tkmt25/chordimouse/circuit/chordimouse.kicad_sch

## KiCad design circuit/chordimouse.kicad_sch (2025-05-18)

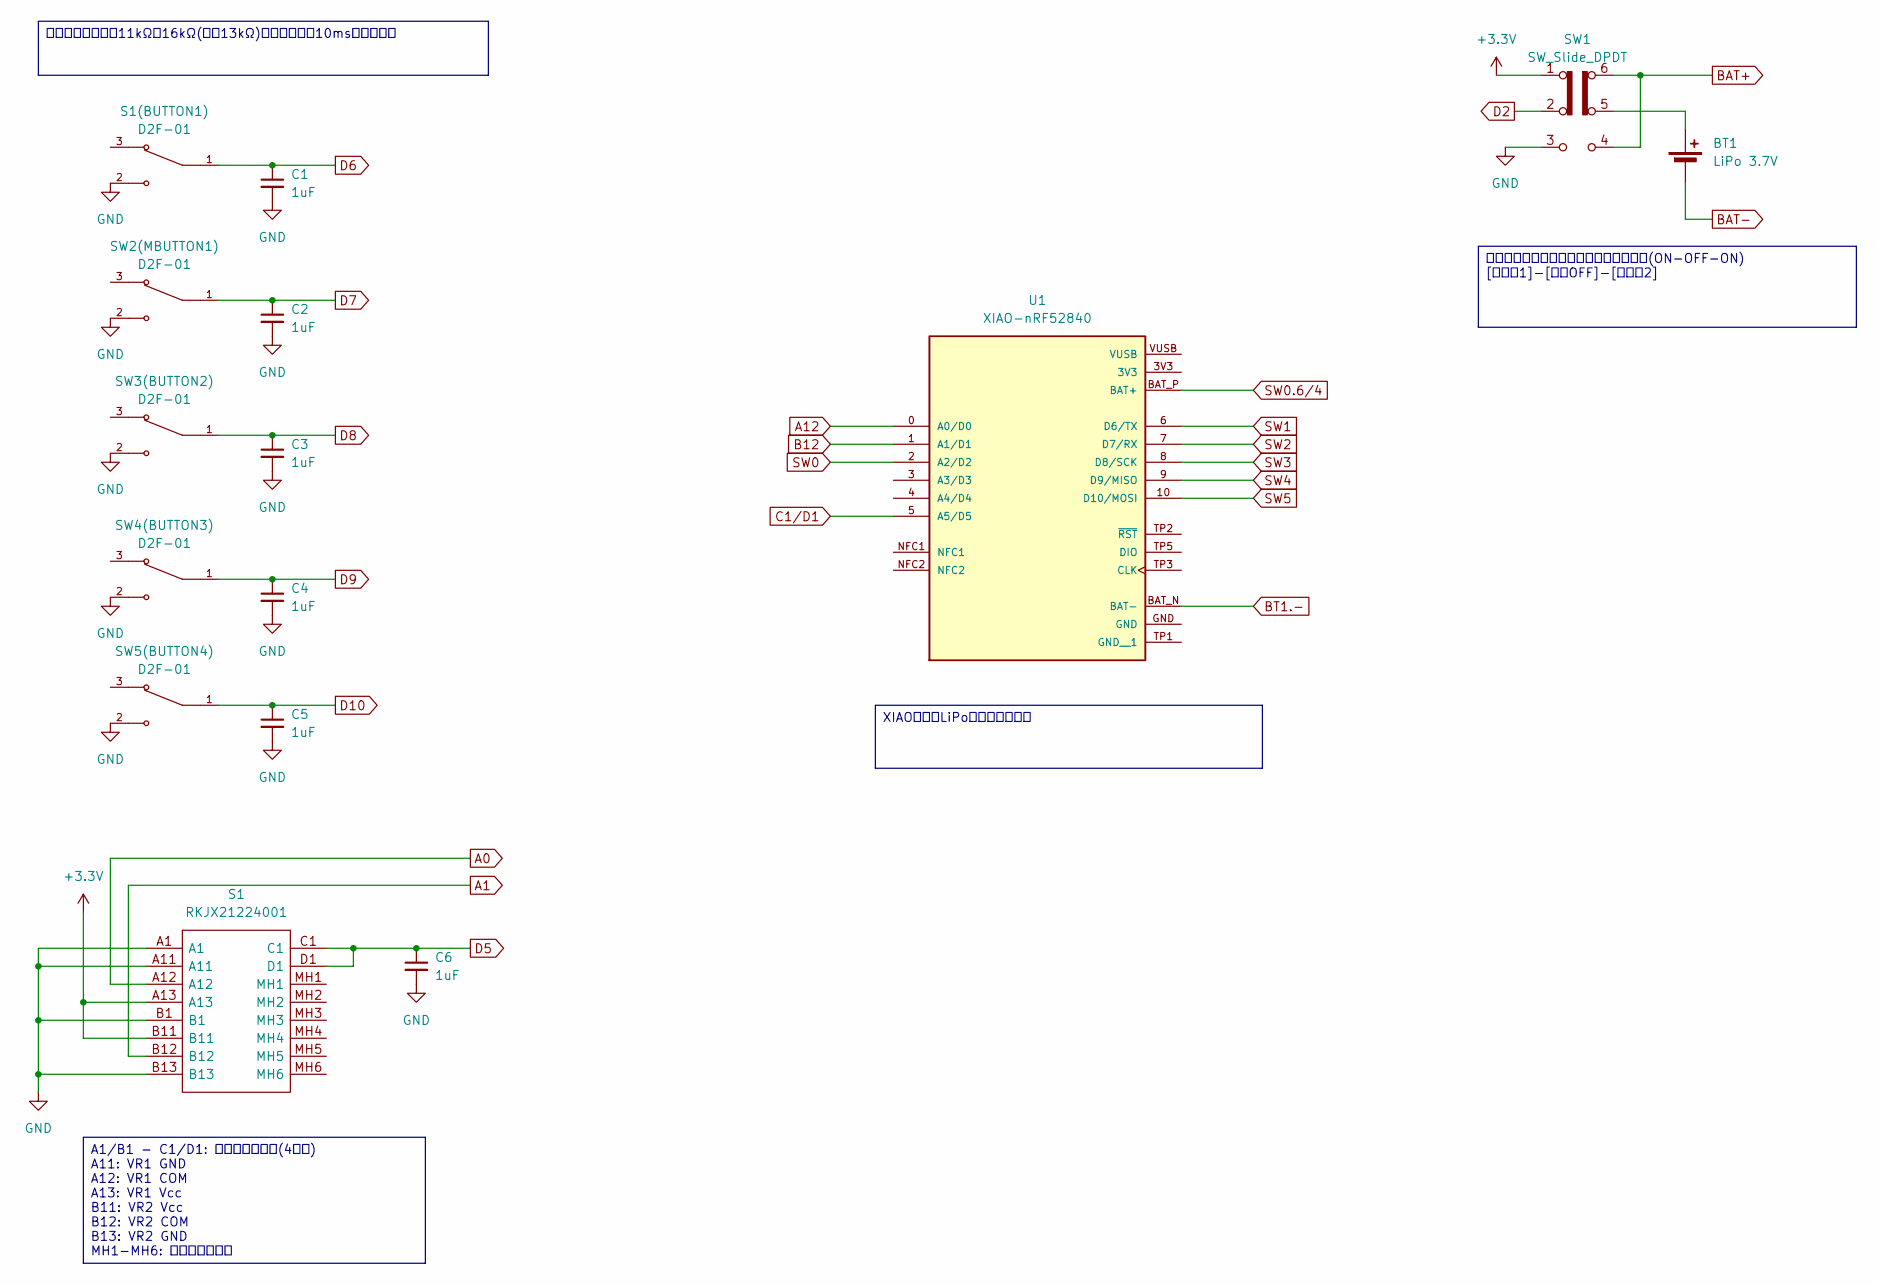
[picture p9: schematic chordimouse.kicad_sch]

Parts:
BT1: LiPo 3.7V
C1, C2, C3, C4, C5, C6: 1uF
S1: RKJX21224001; RKJXV122400R; Manufacturer_Part_Number RKJXV122400R; Mouser Part Number 688-RKJXV122400R
S1(BUTTON1): D2F-01; SW_D2F-01F; PARTREV B036-E1-12
SW1: SW_Slide_DPDT
SW2(MBUTTON1), SW3(BUTTON2), SW4(BUTTON3), SW5(BUTTON4): D2F-01; SW_D2F-01F; PARTREV B036-E1-12
U1: XIAO-nRF52840; MODULE_102010448; PARTREV 2022/08/18

Connections:
+3.3V: S1.A13, S1.B11, SW1.1 (A)
A0: S1.A12
A1: S1.B12
A12: U1.0 (A0/D0)
B12: U1.1 (A1/D1)
BAT+: SW1.4 (A), SW1.6 (C)
BAT-: BT1.2 (-)
BT1.-: U1.BAT_N (BAT-)
C1/D1: U1.5 (A5/D5)
D2: SW1.2 (B)
D5: C6.1, S1.C1, S1.D1
D6: C1.1, S1(BUTTON1).1
D7: C2.1, SW2(MBUTTON1).1
D8: C3.1, SW3(BUTTON2).1
D9: C4.1, SW4(BUTTON3).1
D10: C5.1, SW5(BUTTON4).1
GND: C1.2, C2.2, C3.2, C4.2, C5.2, C6.2, S1.A1, S1.A11, S1.B1, S1.B13, S1(BUTTON1).2, SW1.3 (C), SW2(MBUTTON1).2, SW3(BUTTON2).2, SW4(BUTTON3).2, SW5(BUTTON4).2
unnamed: BT1.1 (+), SW1.5 (B)
SW0: U1.2 (A2/D2)
SW0.6/4: U1.BAT_P (BAT+)
SW1: U1.6 (D6/TX)
SW2: U1.7 (D7/RX)
SW3: U1.8 (D8/SCK)
SW4: U1.9 (D9/MISO)
SW5: U1.10 (D10/MOSI)

Notes on the sheet:
XIAO内蔵のLiPo制御回路を使用
電源および接続先切替スライドスイッチ(ON-OFF-ON) [接続先1]-[電源OFF]-[接続先2]
内部プルアップは11kΩ～16kΩ(標準13kΩ)のため時定数10ms程度とする
A1/B1 - C1/D1: タクトスイッチ(4端子) A11: VR1 GND A12: VR1 COM A13: VR1 Vcc B11: VR2 Vcc B12: VR2 COM B13: VR2 GND MH1-MH6: 取り付け用の足
